PanBabinicz/project-ether/app/ether/src/mqtt_controller.c

#include "mqtt_controller.h"

static void mqtt_controller_log_error_if_nonzero(const char *message, int error_code) 
{
  const char *TAG = "MQTT_CONTROLLER_EVENT_HANDLER";

  if (error_code != 0) {
    ESP_LOGE(TAG, "Last error %s: 0x%x", message, error_code);
  }
}

void mqtt_controller_event_handler(void *handler_args, esp_event_base_t base, 
                                   int32_t event_id, void *event_data) 
{
  const char *TAG = "MQTT_CONTROLLER_EVENT_HANDLER";
  ESP_LOGD(TAG, "Event dispatched from event loop base=%s, event_id=%" PRIi32 "", base, event_id);

  esp_mqtt_event_handle_t event = event_data;
  esp_mqtt_client_handle_t client = event->client;
  int msg_id;

  switch ((esp_mqtt_event_id_t)event_id) {
    case MQTT_EVENT_CONNECTED:
      ESP_LOGI(TAG, "MQTT_EVENT_CONNECTED");
      msg_id = esp_mqtt_client_publish(client, "/topic/qos1", "data_3", 0, 1, 0);
      ESP_LOGI(TAG, "sent publish successful, msg_id=%d", msg_id);

      msg_id = esp_mqtt_client_subscribe(client, "/topic/qos0", 0);
      ESP_LOGI(TAG, "sent subscribe successful, msg_id=%d", msg_id);

      msg_id = esp_mqtt_client_subscribe(client, "/topic/qos1", 1);
      ESP_LOGI(TAG, "sent subscribe successful, msg_id=%d", msg_id);

      msg_id = esp_mqtt_client_unsubscribe(client, "/topic/qos1");
      ESP_LOGI(TAG, "sent unsubscribe successful, msg_id=%d", msg_id);
      break;
    case MQTT_EVENT_DISCONNECTED:
      ESP_LOGI(TAG, "MQTT_EVENT_DISCONNECTED");
      break;

    case MQTT_EVENT_SUBSCRIBED:
      ESP_LOGI(TAG, "MQTT_EVENT_SUBSCRIBED, msg_id=%d", event->msg_id);
      msg_id = esp_mqtt_client_publish(client, "/topic/qos0", "data", 0, 0, 0);
      ESP_LOGI(TAG, "sent publish successful, msg_id=%d", msg_id);
      break;
    case MQTT_EVENT_UNSUBSCRIBED:
      ESP_LOGI(TAG, "MQTT_EVENT_UNSUBSCRIBED, msg_id=%d", event->msg_id);
      break;
    case MQTT_EVENT_PUBLISHED:
      ESP_LOGI(TAG, "MQTT_EVENT_PUBLISHED, msg_id=%d", event->msg_id);
      break;
    case MQTT_EVENT_DATA:
      ESP_LOGI(TAG, "MQTT_EVENT_DATA");
      printf("TOPIC=%.*s\r\n", event->topic_len, event->topic);
      printf("DATA=%.*s\r\n", event->data_len, event->data);
      break;
    case MQTT_EVENT_ERROR:
      ESP_LOGI(TAG, "MQTT_EVENT_ERROR");
      if (event->error_handle->error_type == MQTT_ERROR_TYPE_TCP_TRANSPORT) {
        mqtt_controller_log_error_if_nonzero("reported from esp-tls", event->error_handle->esp_tls_last_esp_err);
        mqtt_controller_log_error_if_nonzero("reported from tls stack", event->error_handle->esp_tls_stack_err);
        mqtt_controller_log_error_if_nonzero("captured as transport's socket errno",  event->error_handle->esp_transport_sock_errno);
        ESP_LOGI(TAG, "Last errno string (%s)", strerror(event->error_handle->esp_transport_sock_errno));
      }
      break;
    default:
      ESP_LOGI(TAG, "Other event id:%d", event->event_id);
      break;
  }
}

mqtt_controller_result_t mqtt_controller_init(mqtt_controller_descriptor_t *mqtt_controller_descriptor) 
{
  if (!mqtt_controller_descriptor) {
    return MQTT_CONTROLLER_RESULT_ERROR;
  }

  mqtt_controller_descriptor->client_handle = esp_mqtt_client_init(&mqtt_controller_descriptor->client_config);
  /* The last argument may be used to pass data to the event handler, in this example mqtt_event_handler */
  esp_mqtt_client_register_event(mqtt_controller_descriptor->client_handle, ESP_EVENT_ANY_ID, mqtt_controller_descriptor->event_handler, NULL);
  esp_mqtt_client_start(mqtt_controller_descriptor->client_handle);

  return MQTT_CONTROLLER_RESULT_SUCCESS;
}
